cw-urn/koiboard/assets/ortho front.png

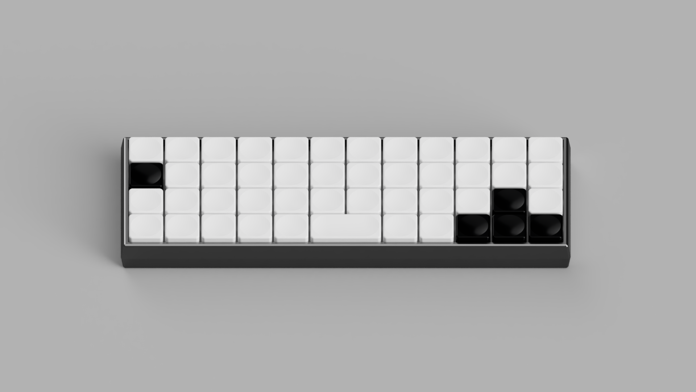
assets/ortho front.png
