cw-urn/koiboard/assets/stasis thumbnail.png

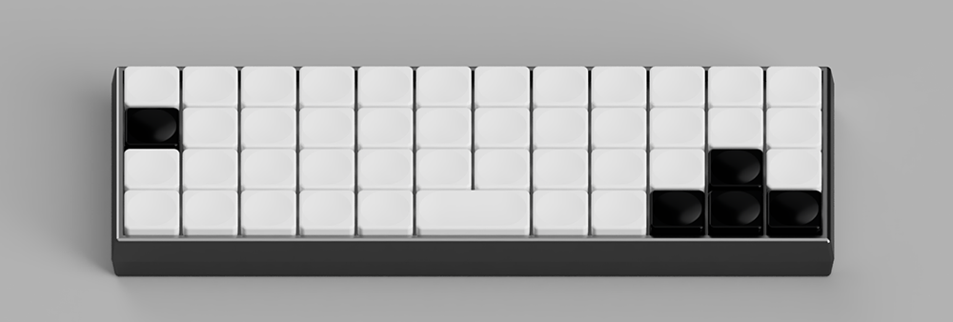
assets/stasis thumbnail.png
