cw-urn/koiboard/assets/webp/IMG_0432.webp

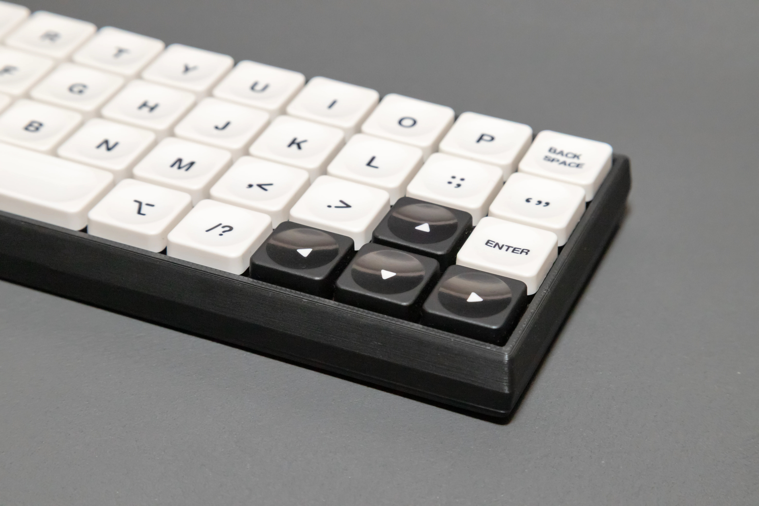
assets/webp/IMG_0432.webp
