cw-urn/koiboard/assets/webp/IMG_0433.webp

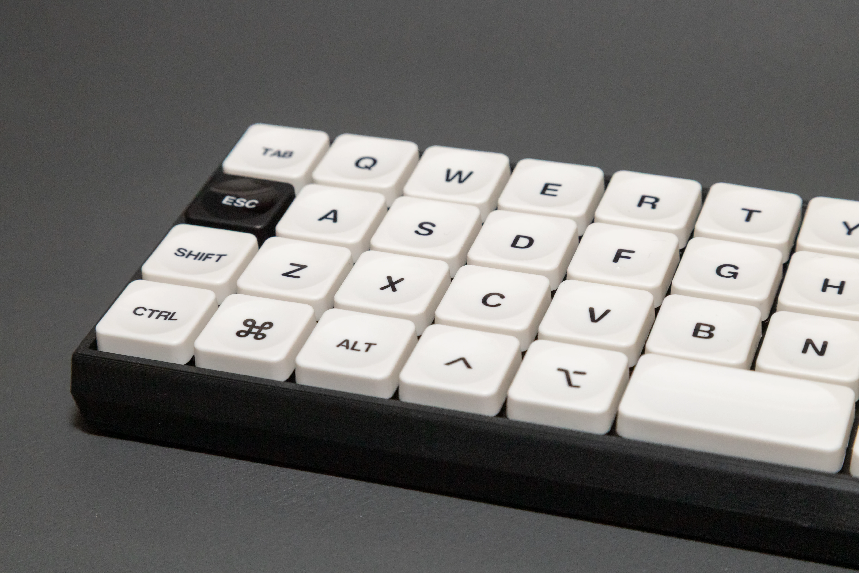
assets/webp/IMG_0433.webp
