cw-urn/koiboard/assets/webp/IMG_0434.webp

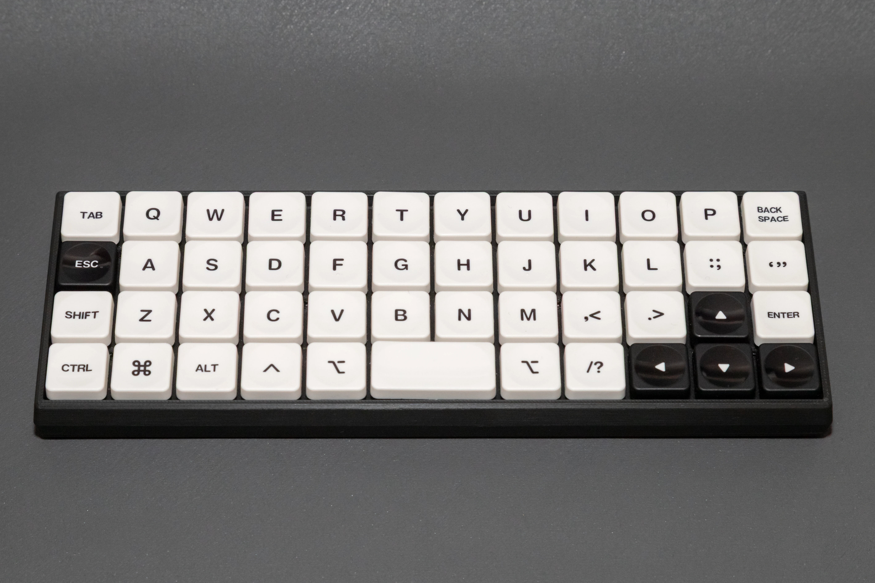
assets/webp/IMG_0434.webp
