cw-urn/koiboard/assets/webp/IMG_0435.webp

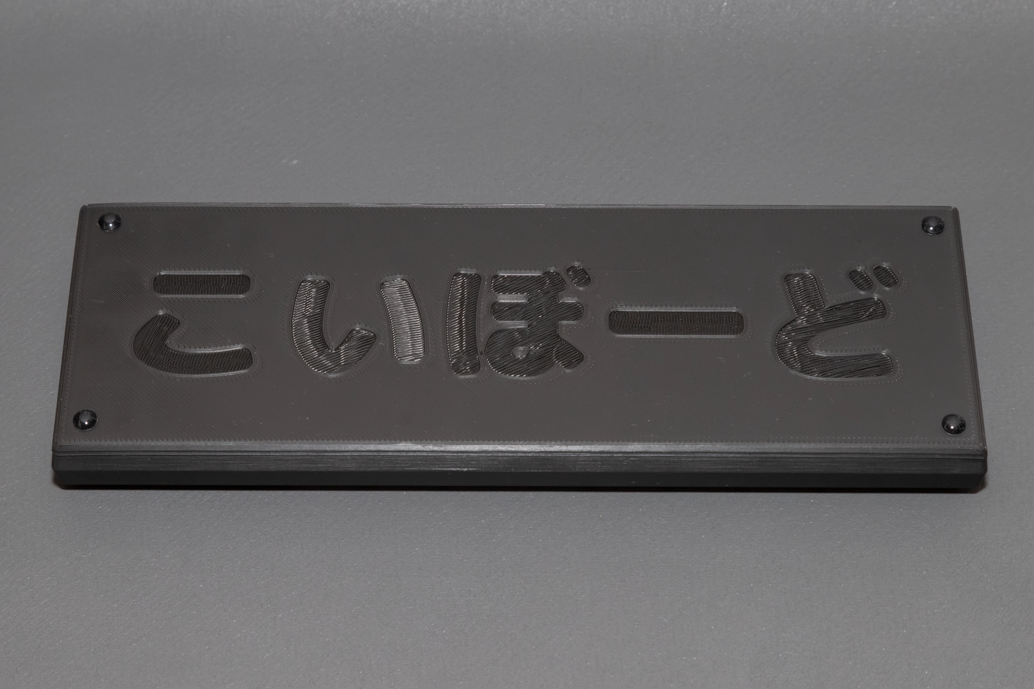
assets/webp/IMG_0435.webp
