cw-urn/koiboard/assets/webp/IMG_0437.webp

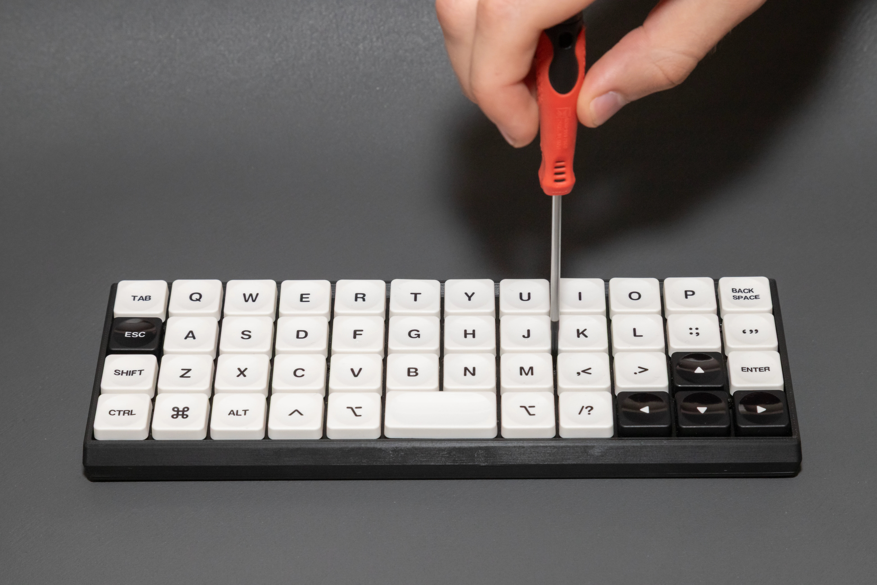
assets/webp/IMG_0437.webp
