cw-urn/koiboard/assets/webp/IMG_0438.webp

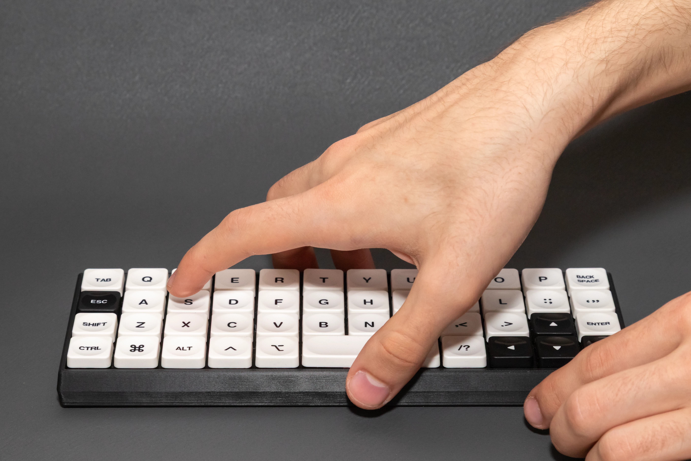
assets/webp/IMG_0438.webp
