cw-urn/koiboard/assets/webp/IMG_0439.webp

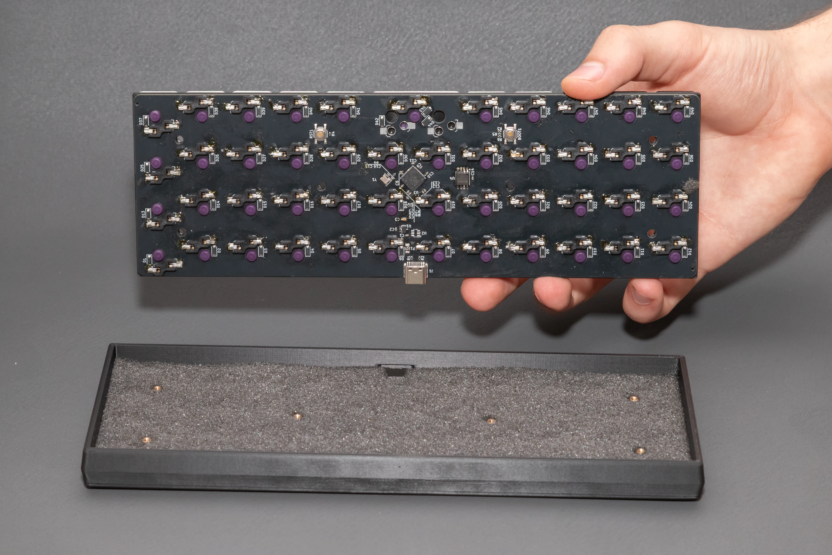
assets/webp/IMG_0439.webp
