cw-urn/koiboard/assets/webp/IMG_0440.webp

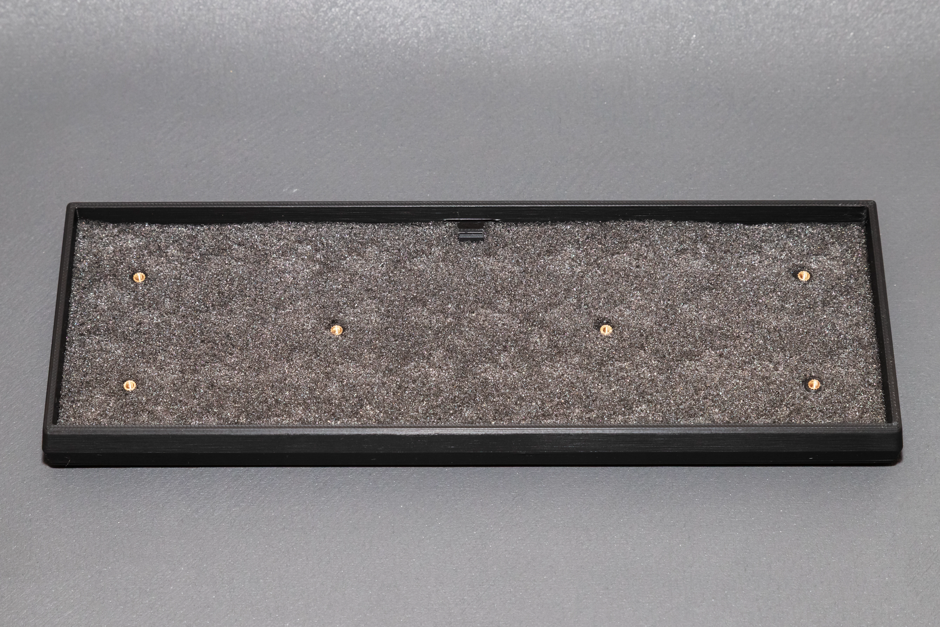
assets/webp/IMG_0440.webp
