cw-urn/koiboard/assets/webp/IMG_0441.webp

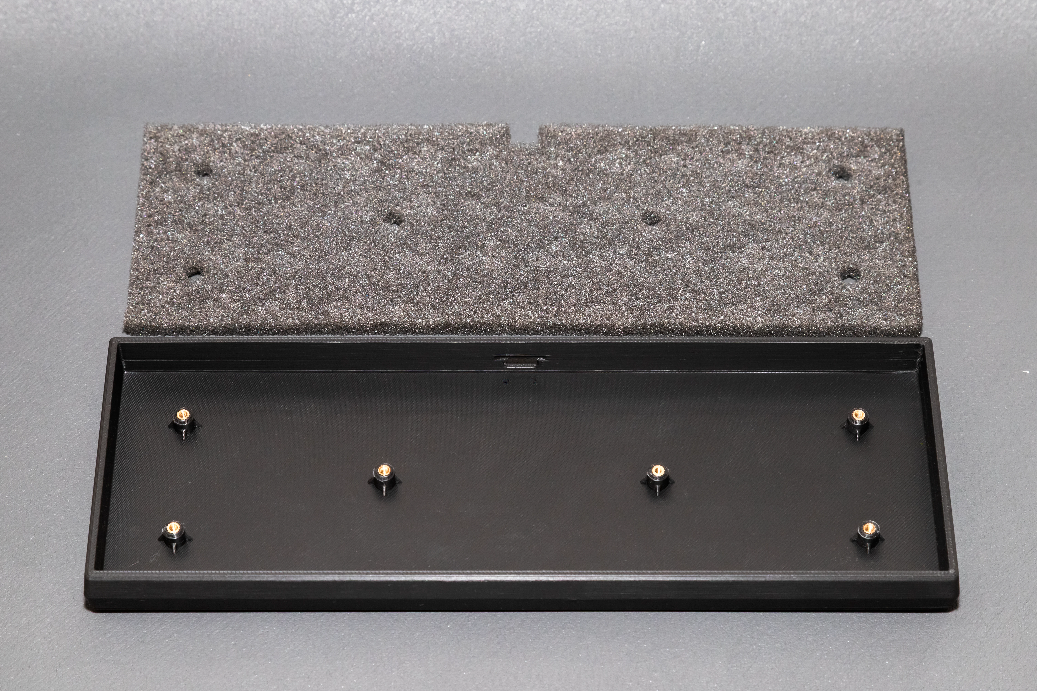
assets/webp/IMG_0441.webp
