cw-urn/koiboard/assets/webp/IMG_0442.webp

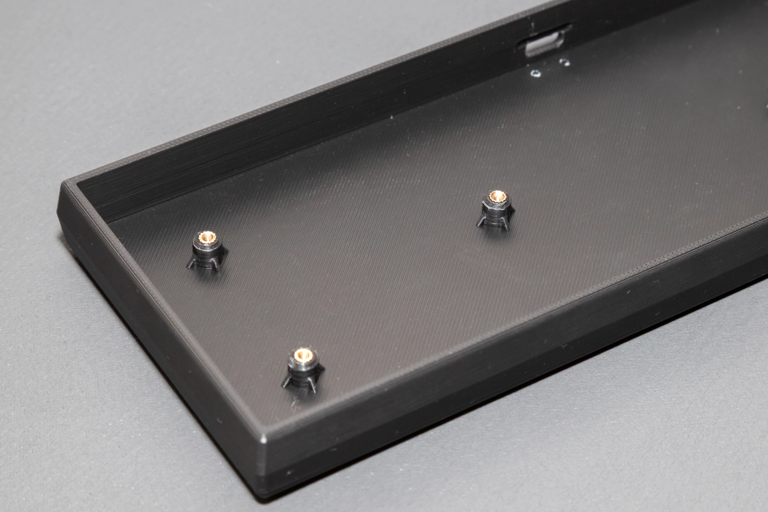
assets/webp/IMG_0442.webp
