cw-urn/koiboard/assets/webp/IMG_0444.webp

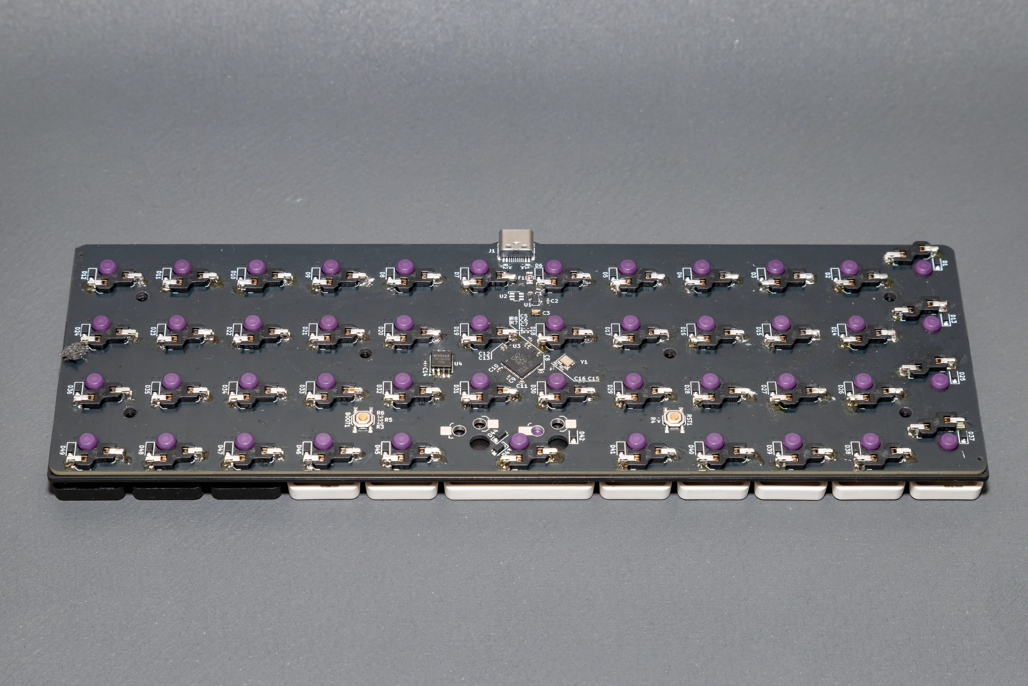
assets/webp/IMG_0444.webp
