cw-urn/koiboard/assets/webp/IMG_0445.webp

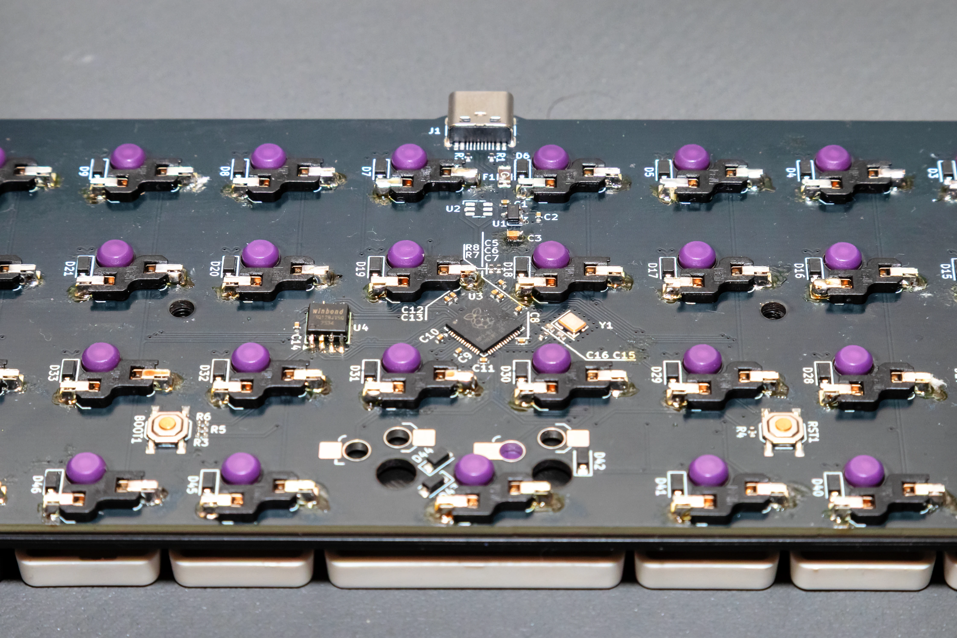
assets/webp/IMG_0445.webp
