cw-urn/koiboard/assets/webp/IMG_0450.webp

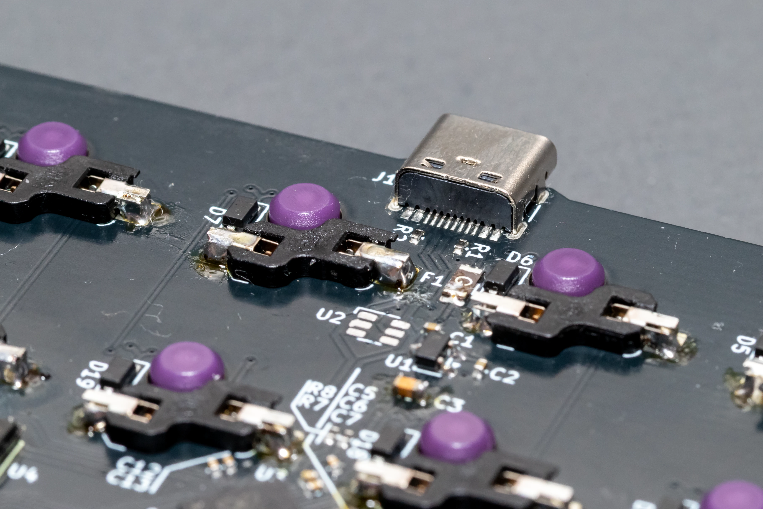
assets/webp/IMG_0450.webp
