cw-urn/koiboard/assets/webp/IMG_0451.webp

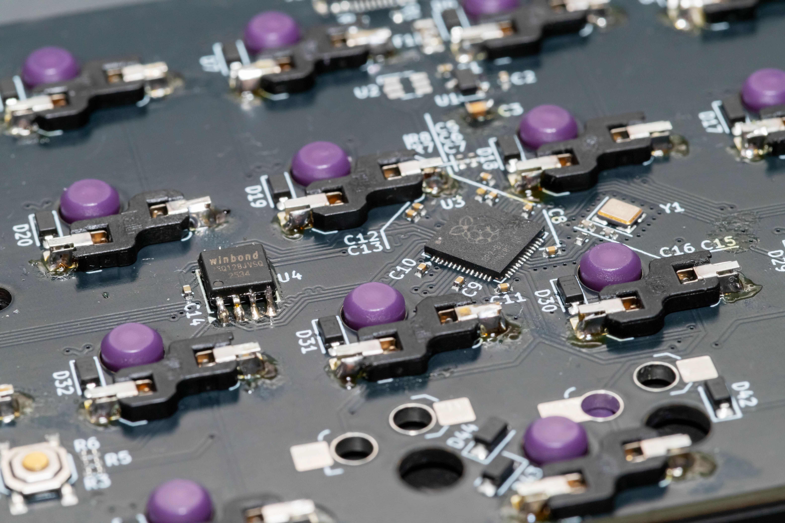
assets/webp/IMG_0451.webp
