cw-urn/koiboard/assets/webp/IMG_0452.webp

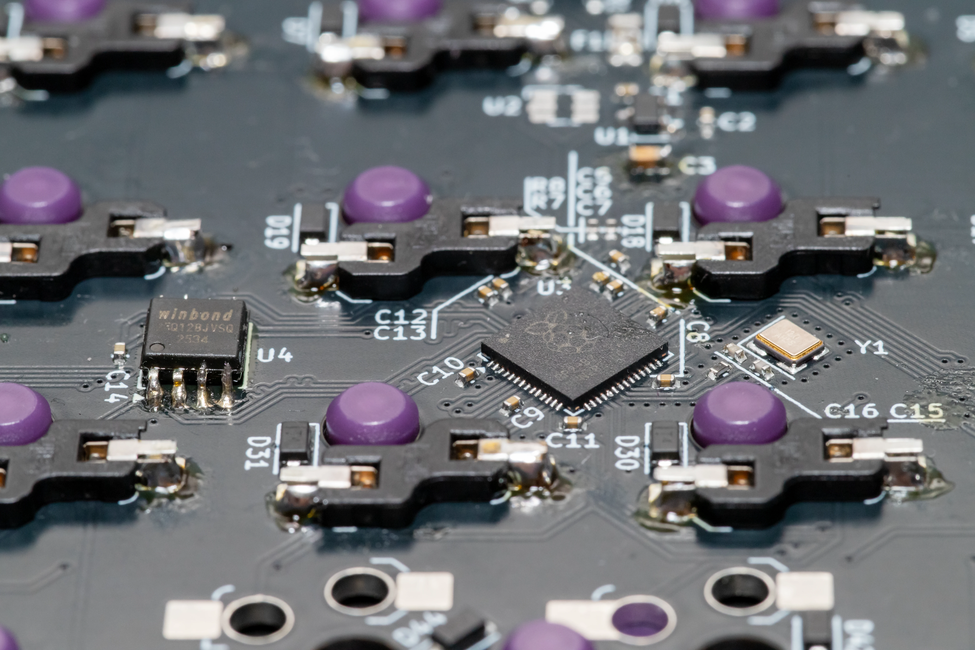
assets/webp/IMG_0452.webp
