cw-urn/koiboard/assets/webp/IMG_0453.webp

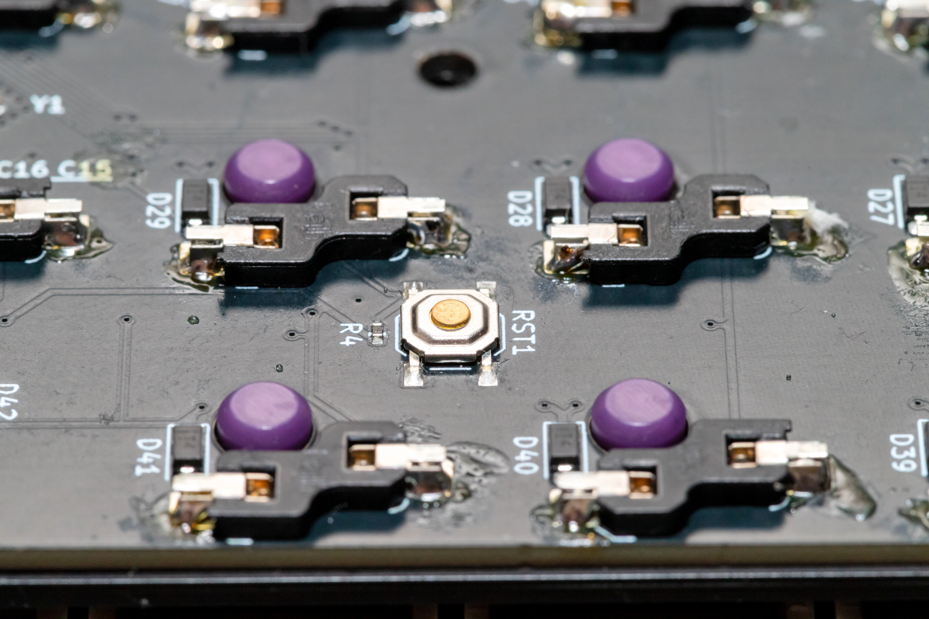
assets/webp/IMG_0453.webp
