cw-urn/koiboard/assets/webp/IMG_0460.webp

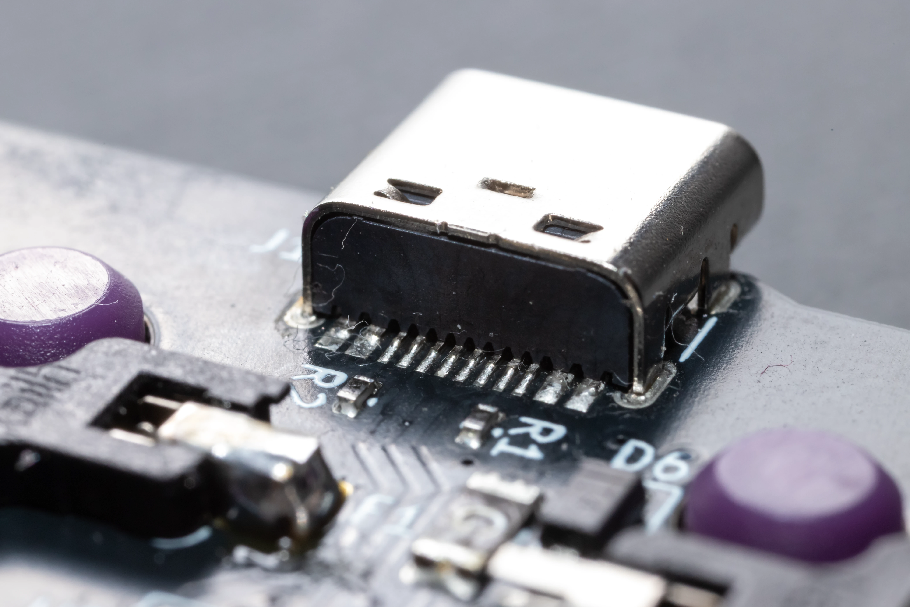
assets/webp/IMG_0460.webp
