cw-urn/koiboard/assets/webp/IMG_0463.webp

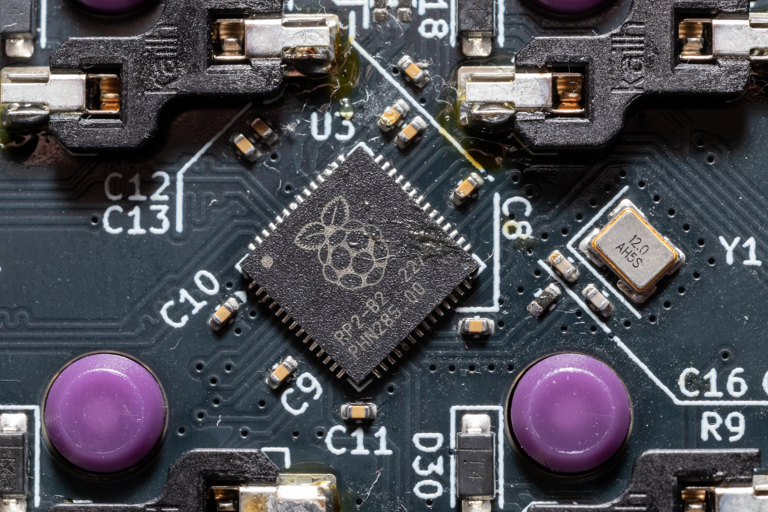
assets/webp/IMG_0463.webp
