cw-urn/koiboard/assets/webp/IMG_0464.webp

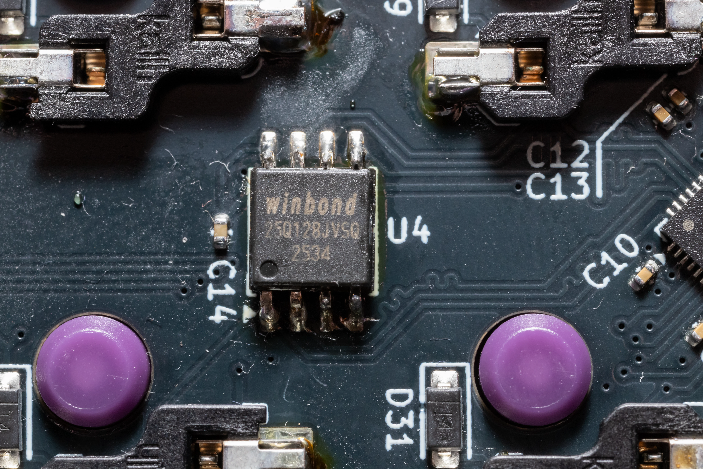
assets/webp/IMG_0464.webp
