cw-urn/koiboard/assets/webp/IMG_0465.webp

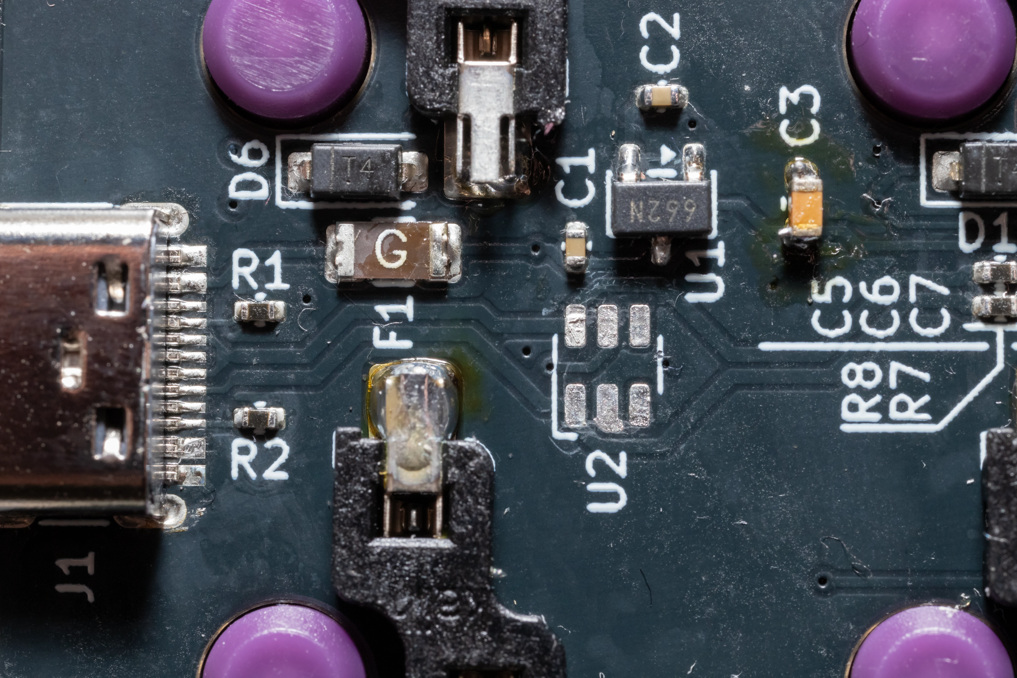
assets/webp/IMG_0465.webp
