cw-urn/koiboard/pcb/documents/C5370443.pdf

# ROHS

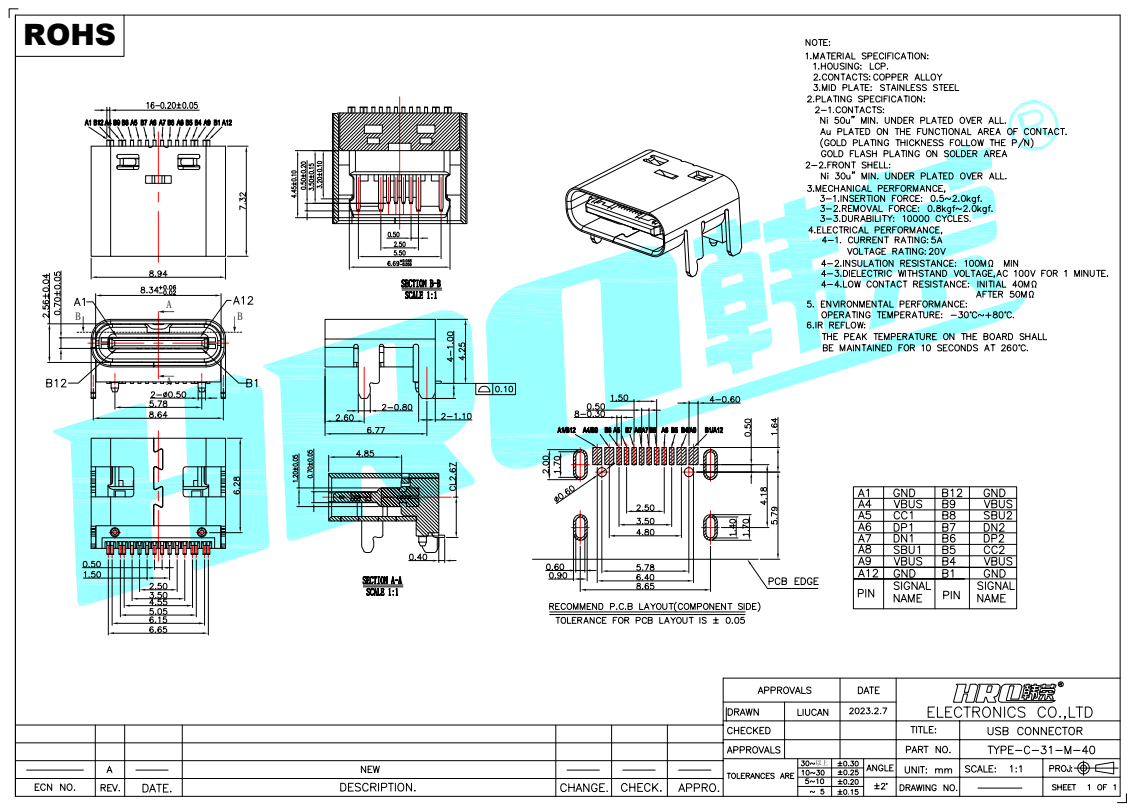
[picture p55: page 1]
